toubippc/TeraCom/include/automation.h

#include "global.h"
#include <iostream>
#include <stdlib.h>
#include <map>


using namespace std;

struct { int relay; int sensors; int value; } devices;
struct { int beginTime; int endTime; int function; } shedules;
// PRAGRAMMATION
struct Temp { int min; int max; };

extern Temp temp1, temp2, temp3, humidity1;
struct Season {
        int beginDD;
        int beginMM;
        int endDD;
        int endMM;
        struct Day {
            int beginH;
            int beginM;
            Temp temp1;
            Temp temp2;
            Temp temp3;
            Temp humidity1;
        } day;
        struct Night {
            int beginH;
            int beginM;
            Temp temp1;
            Temp temp2;
            Temp temp3;
            Temp humidity1;
        } night;
    };

struct Program { 
    Season summer ;
    Season winter ;
};

extern Program program;


#define RELAY_INV 1

#if RELAY_INV == 0
    #define ON 0x1
    #define OFF 0x0
#else
    #define ON 0x0
    #define OFF 0x1
#endif

void automation(void);
void programDefaultValues(void);
