toubippc/TeraCom/include/wpse324.h

//
// This sketch does not use the ALARM registers and uses those 2 bytes as a counter
// these 2 bytes can be used for other purposes as well e.g. last temperature or
// a specific ID.
//
#include "global.h"
#include <OneWire.h>
#include <DallasTemperature.h>

// Data wire is plugged into port 2 on the Arduino
// #define ONE_WIRE_BUS 2

#define COUNT_BUS 2

void wpse324init(void);
void wpse324(void);
